jchitpin/thinkdeck/images/threaded-inserts.jpg

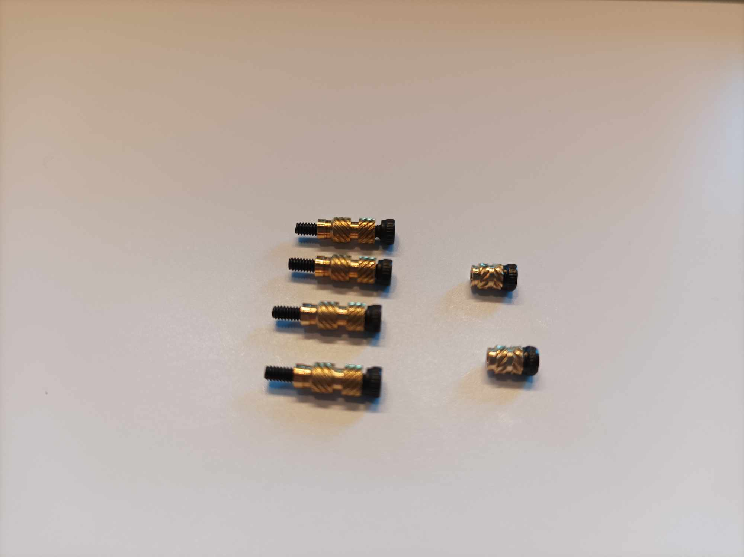
images/threaded-inserts.jpg
